amitpos-gif/project_cpu/mcu - project/DUT/RV32IMscMCU/mcu_system.vhd

-------------------------------------------------------------------------------
-- mcu_system.vhd
-- split to the clock tree and the MCU_top(core + bus interface + peripherals)
-------------------------------------------------------------------------------
library ieee;
use ieee.std_logic_1164.all;
use work.aux_package.all;

entity mcu_system is
    port (
        CLOCK_50 : in  std_logic;                     -- 50 MHz board oscillator
        KEY0     : in  std_logic;                     -- system RESET, active low
        KEY1     : in  std_logic;
        KEY2     : in  std_logic;
        KEY3     : in  std_logic;
        CAPIN1   : in  std_logic;
        CAPIN2   : in  std_logic;

        SW       : in  std_logic_vector(7 downto 0);  -- SW7-SW0
        LEDR     : out std_logic_vector(7 downto 0);  -- LEDR7-LEDR0
        PWM      : out std_logic;
        HEX0     : out std_logic_vector(6 downto 0);
        HEX1     : out std_logic_vector(6 downto 0);
        HEX2     : out std_logic_vector(6 downto 0);
        HEX3     : out std_logic_vector(6 downto 0);
        HEX4     : out std_logic_vector(6 downto 0);
        HEX5     : out std_logic_vector(6 downto 0)
    );
end entity mcu_system;

architecture structural of mcu_system is

    signal mclk_w     : std_logic;
    signal accelclk_w : std_logic;
    signal smclk_w    : std_logic;
    signal locked_w   : std_logic;

    signal key0_rst_w : std_logic;   -- KEY0 inverted to active high
    signal rst_w      : std_logic;   -- system reset, active high

begin

    ----------------------------------------------------------------
    -- Reset: KEY0 is active low, the design is active high. Reset is
    -- also held while the PLL has not locked.
    ----------------------------------------------------------------
    key0_rst_w <= not KEY0;
    rst_w      <= key0_rst_w or (not locked_w);

    ----------------------------------------------------------------
    -- Clock Tree (Figure 1)
    ----------------------------------------------------------------
    CLKTREE : clock_tree
        port map (
            rst_i      => key0_rst_w,   -- not gated by locked, it generates it
            baseclk_i  => CLOCK_50,
            mclk_o     => mclk_w,
            accelclk_o => accelclk_w,
            smclk_o    => smclk_w,
            locked_o   => locked_w
        );

    ----------------------------------------------------------------
    -- MCU (Figure 1: core + bus interface + peripherals)
    ----------------------------------------------------------------
    MCU : mcu_top
        port map (
            rst_i    => rst_w,
            clk_i    => mclk_w,
            divclk_i => accelclk_w,
            smclk    => smclk_w,
            KEY1     => KEY1,
            KEY2     => KEY2,
            KEY3     => KEY3,
            CAPIN1   => CAPIN1,
            CAPIN2   => CAPIN2,
            SW       => SW,
            LEDR     => LEDR,
            PWM      => PWM,
            HEX0     => HEX0,
            HEX1     => HEX1,
            HEX2     => HEX2,
            HEX3     => HEX3,
            HEX4     => HEX4,
            HEX5     => HEX5
        );

end architecture structural;
